wkmilanswanthra/Rubber-Mixer-Machine/NImz/KeyPad Fking Last/GccApplicationxx/GccApplicationxx/types.h

/*
 * types.h
 *
 * Created: 9/22/2016 7:09:15 PM
 *  Author: WALY
 */ 

#ifndef TYPES_H_
#define TYPES_H_

typedef unsigned char uint8;
typedef signed char sint8;
typedef unsigned short uint16;
typedef signed short sint16;
typedef unsigned long uint32;
typedef signed long sint32;
typedef unsigned long long uint64;
typedef signed long long sint64;
enum Boolen {true=1,false=0};

#endif
