wkmilanswanthra/Rubber-Mixer-Machine/test2/keypad2.h

#ifndef KEYPAD_H_
#define KEYPAD_H_

/******************standard libraries*****************/
#include <stdint.h>
/************************Libraries********************/
#include "keypadconfig.h"


#define ALL_LINES   (((LINE0_PIN&(1U<<LINE0))>>LINE0)&((LINE1_PIN&(1U<<LINE1))>>LINE1)&((LINE2_PIN&(1U<<LINE2))>>LINE2)&((LINE3_PIN&(1U<<LINE3))>>LINE3))
 
void keypad_init(void);
uint8_t keypad_scan(void);



#endif // KEYPAD_H_
